roboticsuic/UIC-duino-hand/3D files/images/arm.jpg

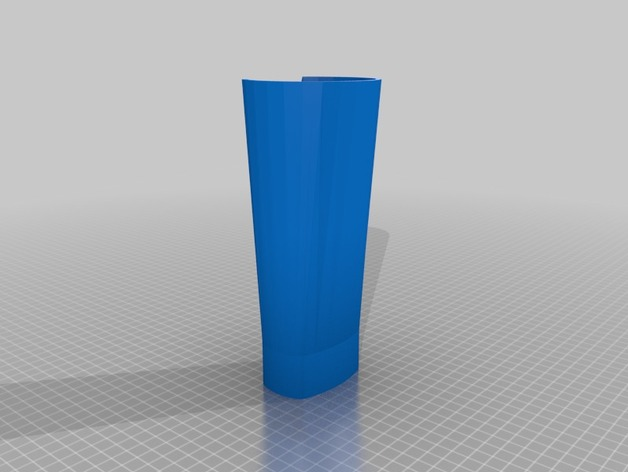
3D files/images/arm.jpg
