roboticsuic/UIC-duino-hand/3D files/LH_Finger_Plate.stl

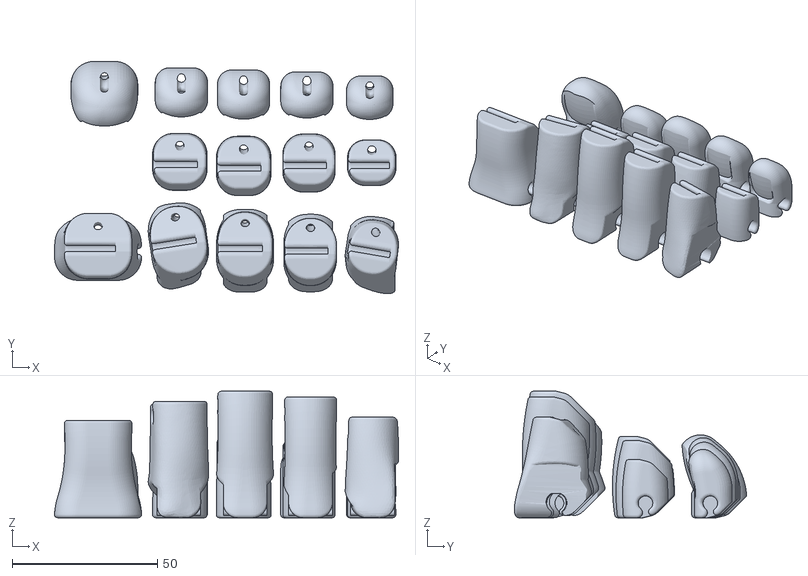
[picture p26: CAD file, 2020-03-03]
3D files/LH_Finger_Plate.stl
118.3 x 79.9 x 43.5
