roboticsuic/UIC-duino-hand/3D files/images/guidetubedesignneedstobechanged.png

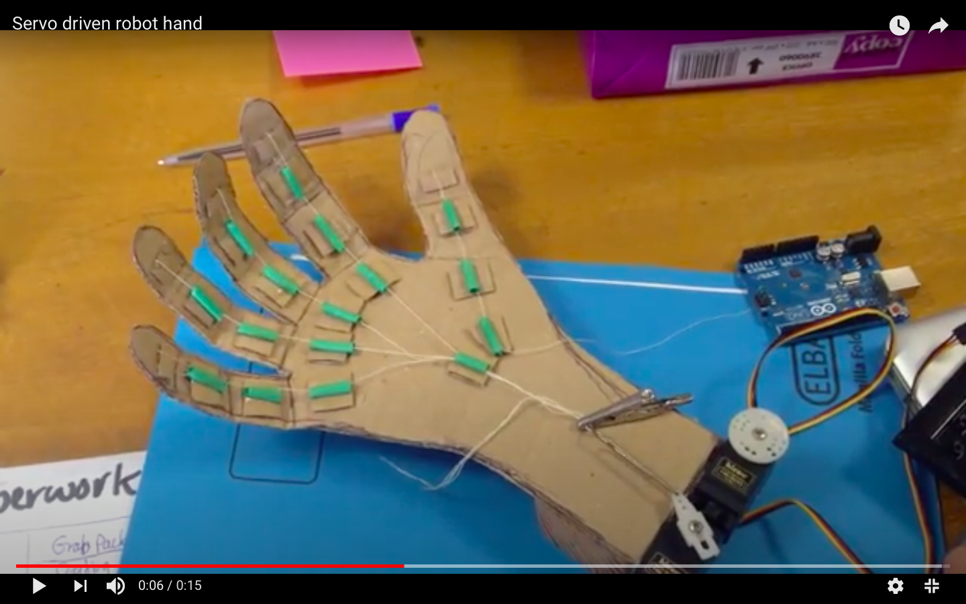
3D files/images/guidetubedesignneedstobechanged.png
