roboticsuic/UIC-duino-hand/3D files/images/scheme box ensamble view 3.PNG

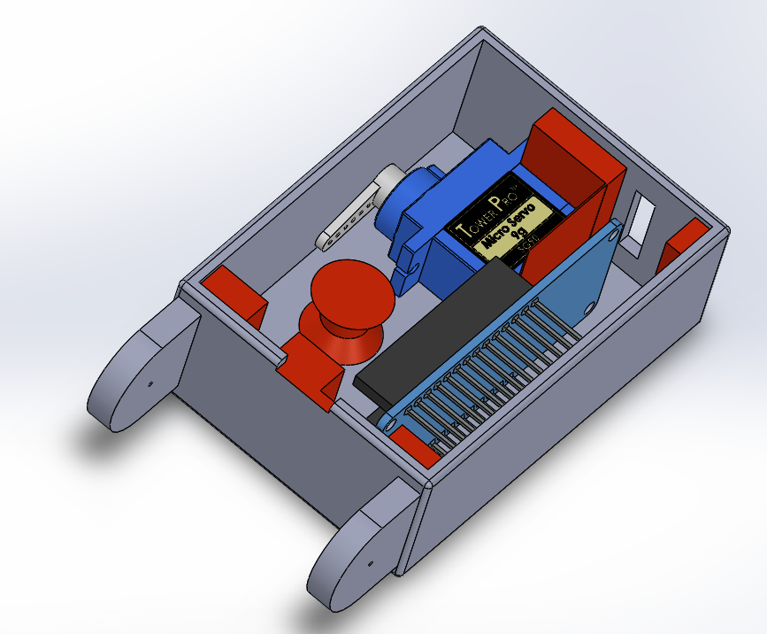
3D files/images/scheme box ensamble view 3.PNG
